Danjovic/JoyKid/sources/PIC/JoyKidProtocol/Test/pic16f688.h

/*
 * This declarations of the PIC16F688 MCU.
 *
 * This file is part of the GNU PIC library for SDCC, originally
 * created by Molnar Karoly <molnarkaroly@users.sf.net> 2012.
 *
 * This file is generated automatically by the cinc2h.pl, 2012-11-01 17:30:08 UTC.
 *
 * SDCC is licensed under the GNU Public license (GPL) v2. Note that
 * this license covers the code to the compiler and other executables,
 * but explicitly does not cover any code or objects generated by sdcc.
 *
 * For pic device libraries and header files which are derived from
 * Microchip header (.inc) and linker script (.lkr) files Microchip
 * requires that "The header files should state that they are only to be
 * used with authentic Microchip devices" which makes them incompatible
 * with the GPL. Pic device libraries and header files are located at
 * non-free/lib and non-free/include directories respectively.
 * Sdcc should be run with the --use-non-free command line option in
 * order to include non-free header files and libraries.
 *
 * See http://sdcc.sourceforge.net/ for the latest information on sdcc.
 */

#ifndef __PIC16F688_H__
#define __PIC16F688_H__

//==============================================================================
//
//	Register Addresses
//
//==============================================================================

#ifndef NO_ADDR_DEFINES

#define INDF_ADDR               0x0000
#define TMR0_ADDR               0x0001
#define PCL_ADDR                0x0002
#define STATUS_ADDR             0x0003
#define FSR_ADDR                0x0004
#define PORTA_ADDR              0x0005
#define PORTC_ADDR              0x0007
#define PCLATH_ADDR             0x000A
#define INTCON_ADDR             0x000B
#define PIR1_ADDR               0x000C
#define TMR1_ADDR               0x000E
#define TMR1L_ADDR              0x000E
#define TMR1H_ADDR              0x000F
#define T1CON_ADDR              0x0010
#define BAUDCTL_ADDR            0x0011
#define SPBRGH_ADDR             0x0012
#define SPBRG_ADDR              0x0013
#define RCREG_ADDR              0x0014
#define TXREG_ADDR              0x0015
#define TXSTA_ADDR              0x0016
#define RCSTA_ADDR              0x0017
#define WDTCON_ADDR             0x0018
#define CMCON0_ADDR             0x0019
#define CMCON1_ADDR             0x001A
#define ADRESH_ADDR             0x001E
#define ADCON0_ADDR             0x001F
#define OPTION_REG_ADDR         0x0081
#define TRISA_ADDR              0x0085
#define TRISC_ADDR              0x0087
#define PIE1_ADDR               0x008C
#define PCON_ADDR               0x008E
#define OSCCON_ADDR             0x008F
#define OSCTUNE_ADDR            0x0090
#define ANSEL_ADDR              0x0091
#define WPU_ADDR                0x0095
#define WPUA_ADDR               0x0095
#define IOC_ADDR                0x0096
#define IOCA_ADDR               0x0096
#define EEDATH_ADDR             0x0097
#define EEADRH_ADDR             0x0098
#define VRCON_ADDR              0x0099
#define EEDAT_ADDR              0x009A
#define EEDATA_ADDR             0x009A
#define EEADR_ADDR              0x009B
#define EECON1_ADDR             0x009C
#define EECON2_ADDR             0x009D
#define ADRESL_ADDR             0x009E
#define ADCON1_ADDR             0x009F

#endif // #ifndef NO_ADDR_DEFINES

//==============================================================================
//
//	Register Definitions
//
//==============================================================================

extern __at(0x0000) __sfr INDF;
extern __at(0x0001) __sfr TMR0;
extern __at(0x0002) __sfr PCL;

//==============================================================================
//        STATUS Bits

extern __at(0x0003) __sfr STATUS;

typedef union
  {
  struct
    {
    unsigned C                  : 1;
    unsigned DC                 : 1;
    unsigned Z                  : 1;
    unsigned NOT_PD             : 1;
    unsigned NOT_TO             : 1;
    unsigned RP0                : 1;
    unsigned RP1                : 1;
    unsigned IRP                : 1;
    };

  struct
    {
    unsigned                    : 5;
    unsigned RP                 : 2;
    unsigned                    : 1;
    };
  } __STATUSbits_t;

extern __at(0x0003) volatile __STATUSbits_t STATUSbits;

#define _C                      0x01
#define _DC                     0x02
#define _Z                      0x04
#define _NOT_PD                 0x08
#define _NOT_TO                 0x10
#define _RP0                    0x20
#define _RP1                    0x40
#define _IRP                    0x80

//==============================================================================

extern __at(0x0004) __sfr FSR;

//==============================================================================
//        PORTA Bits

extern __at(0x0005) __sfr PORTA;

typedef union
  {
  struct
    {
    unsigned RA0                : 1;
    unsigned RA1                : 1;
    unsigned RA2                : 1;
    unsigned RA3                : 1;
    unsigned RA4                : 1;
    unsigned RA5                : 1;
    unsigned                    : 1;
    unsigned                    : 1;
    };

  struct
    {
    unsigned RA                 : 6;
    unsigned                    : 2;
    };
  } __PORTAbits_t;

extern __at(0x0005) volatile __PORTAbits_t PORTAbits;

#define _RA0                    0x01
#define _RA1                    0x02
#define _RA2                    0x04
#define _RA3                    0x08
#define _RA4                    0x10
#define _RA5                    0x20

//==============================================================================


//==============================================================================
//        PORTC Bits

extern __at(0x0007) __sfr PORTC;

typedef union
  {
  struct
    {
    unsigned RC0                : 1;
    unsigned RC1                : 1;
    unsigned RC2                : 1;
    unsigned RC3                : 1;
    unsigned RC4                : 1;
    unsigned RC5                : 1;
    unsigned                    : 1;
    unsigned                    : 1;
    };

  struct
    {
    unsigned RC                 : 6;
    unsigned                    : 2;
    };
  } __PORTCbits_t;

extern __at(0x0007) volatile __PORTCbits_t PORTCbits;

#define _RC0                    0x01
#define _RC1                    0x02
#define _RC2                    0x04
#define _RC3                    0x08
#define _RC4                    0x10
#define _RC5                    0x20

//==============================================================================

extern __at(0x000A) __sfr PCLATH;

//==============================================================================
//        INTCON Bits

extern __at(0x000B) __sfr INTCON;

typedef union
  {
  struct
    {
    unsigned RAIF               : 1;
    unsigned INTF               : 1;
    unsigned T0IF               : 1;
    unsigned RAIE               : 1;
    unsigned INTE               : 1;
    unsigned T0IE               : 1;
    unsigned PEIE               : 1;
    unsigned GIE                : 1;
    };

  struct
    {
    unsigned                    : 1;
    unsigned                    : 1;
    unsigned TMR0IF             : 1;
    unsigned                    : 1;
    unsigned                    : 1;
    unsigned TMR0IE             : 1;
    unsigned                    : 1;
    unsigned                    : 1;
    };
  } __INTCONbits_t;

extern __at(0x000B) volatile __INTCONbits_t INTCONbits;

#define _RAIF                   0x01
#define _INTF                   0x02
#define _T0IF                   0x04
#define _TMR0IF                 0x04
#define _RAIE                   0x08
#define _INTE                   0x10
#define _T0IE                   0x20
#define _TMR0IE                 0x20
#define _PEIE                   0x40
#define _GIE                    0x80

//==============================================================================


//==============================================================================
//        PIR1 Bits

extern __at(0x000C) __sfr PIR1;

typedef union
  {
  struct
    {
    unsigned TMR1IF             : 1;
    unsigned TXIF               : 1;
    unsigned OSFIF              : 1;
    unsigned C1IF               : 1;
    unsigned C2IF               : 1;
    unsigned RCIF               : 1;
    unsigned ADIF               : 1;
    unsigned EEIF               : 1;
    };

  struct
    {
    unsigned T1IF               : 1;
    unsigned                    : 1;
    unsigned                    : 1;
    unsigned                    : 1;
    unsigned                    : 1;
    unsigned                    : 1;
    unsigned                    : 1;
    unsigned                    : 1;
    };
  } __PIR1bits_t;

extern __at(0x000C) volatile __PIR1bits_t PIR1bits;

#define _TMR1IF                 0x01
#define _T1IF                   0x01
#define _TXIF                   0x02
#define _OSFIF                  0x04
#define _C1IF                   0x08
#define _C2IF                   0x10
#define _RCIF                   0x20
#define _ADIF                   0x40
#define _EEIF                   0x80

//==============================================================================

extern __at(0x000E) __sfr TMR1;
extern __at(0x000E) __sfr TMR1L;
extern __at(0x000F) __sfr TMR1H;

//==============================================================================
//        T1CON Bits

extern __at(0x0010) __sfr T1CON;

typedef union
  {
  struct
    {
    unsigned TMR1ON             : 1;
    unsigned TMR1CS             : 1;
    unsigned NOT_T1SYNC         : 1;
    unsigned T1OSCEN            : 1;
    unsigned T1CKPS0            : 1;
    unsigned T1CKPS1            : 1;
    unsigned TMR1GE             : 1;
    unsigned T1GINV             : 1;
    };

  struct
    {
    unsigned                    : 4;
    unsigned T1CKPS             : 2;
    unsigned                    : 2;
    };
  } __T1CONbits_t;

extern __at(0x0010) volatile __T1CONbits_t T1CONbits;

#define _TMR1ON                 0x01
#define _TMR1CS                 0x02
#define _NOT_T1SYNC             0x04
#define _T1OSCEN                0x08
#define _T1CKPS0                0x10
#define _T1CKPS1                0x20
#define _TMR1GE                 0x40
#define _T1GINV                 0x80

//==============================================================================


//==============================================================================
//        BAUDCTL Bits

extern __at(0x0011) __sfr BAUDCTL;

#define BAUDCON BAUDCTL

typedef struct
  {
  unsigned ABDEN                : 1;
  unsigned WUE                  : 1;
  unsigned                      : 1;
  unsigned BRG16                : 1;
  unsigned SCKP                 : 1;
  unsigned                      : 1;
  unsigned RCIDL                : 1;
  unsigned ABDOVF               : 1;
  } __BAUDCTLbits_t;

extern __at(0x0011) volatile __BAUDCTLbits_t BAUDCTLbits;

#define BAUDCONbits BAUDCTLbits

#define _ABDEN                  0x01
#define _WUE                    0x02
#define _BRG16                  0x08
#define _SCKP                   0x10
#define _RCIDL                  0x40
#define _ABDOVF                 0x80

//==============================================================================

extern __at(0x0012) __sfr SPBRGH;
extern __at(0x0013) __sfr SPBRG;
extern __at(0x0014) __sfr RCREG;
extern __at(0x0015) __sfr TXREG;

//==============================================================================
//        TXSTA Bits

extern __at(0x0016) __sfr TXSTA;

typedef struct
  {
  unsigned TX9D                 : 1;
  unsigned TRMT                 : 1;
  unsigned BRGH                 : 1;
  unsigned SENDB                : 1;
  unsigned SYNC                 : 1;
  unsigned TXEN                 : 1;
  unsigned TX9                  : 1;
  unsigned CSRC                 : 1;
  } __TXSTAbits_t;

extern __at(0x0016) volatile __TXSTAbits_t TXSTAbits;

#define _TX9D                   0x01
#define _TRMT                   0x02
#define _BRGH                   0x04
#define _SENDB                  0x08
#define _SYNC                   0x10
#define _TXEN                   0x20
#define _TX9                    0x40
#define _CSRC                   0x80

//==============================================================================


//==============================================================================
//        RCSTA Bits

extern __at(0x0017) __sfr RCSTA;

typedef struct
  {
  unsigned RX9D                 : 1;
  unsigned OERR                 : 1;
  unsigned FERR                 : 1;
  unsigned ADDEN                : 1;
  unsigned CREN                 : 1;
  unsigned SREN                 : 1;
  unsigned RX9                  : 1;
  unsigned SPEN                 : 1;
  } __RCSTAbits_t;

extern __at(0x0017) volatile __RCSTAbits_t RCSTAbits;

#define _RX9D                   0x01
#define _OERR                   0x02
#define _FERR                   0x04
#define _ADDEN                  0x08
#define _CREN                   0x10
#define _SREN                   0x20
#define _RX9                    0x40
#define _SPEN                   0x80

//==============================================================================


//==============================================================================
//        WDTCON Bits

extern __at(0x0018) __sfr WDTCON;

typedef union
  {
  struct
    {
    unsigned SWDTEN             : 1;
    unsigned WDTPS0             : 1;
    unsigned WDTPS1             : 1;
    unsigned WDTPS2             : 1;
    unsigned WDTPS3             : 1;
    unsigned                    : 1;
    unsigned                    : 1;
    unsigned                    : 1;
    };

  struct
    {
    unsigned                    : 1;
    unsigned WDTPS              : 4;
    unsigned                    : 3;
    };
  } __WDTCONbits_t;

extern __at(0x0018) volatile __WDTCONbits_t WDTCONbits;

#define _SWDTEN                 0x01
#define _WDTPS0                 0x02
#define _WDTPS1                 0x04
#define _WDTPS2                 0x08
#define _WDTPS3                 0x10

//==============================================================================


//==============================================================================
//        CMCON0 Bits

extern __at(0x0019) __sfr CMCON0;

typedef union
  {
  struct
    {
    unsigned CM0                : 1;
    unsigned CM1                : 1;
    unsigned CM2                : 1;
    unsigned CIS                : 1;
    unsigned C1INV              : 1;
    unsigned C2INV              : 1;
    unsigned C1OUT              : 1;
    unsigned C2OUT              : 1;
    };

  struct
    {
    unsigned CM                 : 3;
    unsigned                    : 5;
    };
  } __CMCON0bits_t;

extern __at(0x0019) volatile __CMCON0bits_t CMCON0bits;

#define _CM0                    0x01
#define _CM1                    0x02
#define _CM2                    0x04
#define _CIS                    0x08
#define _C1INV                  0x10
#define _C2INV                  0x20
#define _C1OUT                  0x40
#define _C2OUT                  0x80

//==============================================================================


//==============================================================================
//        CMCON1 Bits

extern __at(0x001A) __sfr CMCON1;

typedef struct
  {
  unsigned C2SYNC               : 1;
  unsigned T1GSS                : 1;
  unsigned                      : 1;
  unsigned                      : 1;
  unsigned                      : 1;
  unsigned                      : 1;
  unsigned                      : 1;
  unsigned                      : 1;
  } __CMCON1bits_t;

extern __at(0x001A) volatile __CMCON1bits_t CMCON1bits;

#define _C2SYNC                 0x01
#define _T1GSS                  0x02

//==============================================================================

extern __at(0x001E) __sfr ADRESH;

//==============================================================================
//        ADCON0 Bits

extern __at(0x001F) __sfr ADCON0;

typedef union
  {
  struct
    {
    unsigned ADON               : 1;
    unsigned GO_NOT_DONE        : 1;
    unsigned CHS0               : 1;
    unsigned CHS1               : 1;
    unsigned CHS2               : 1;
    unsigned                    : 1;
    unsigned VCFG               : 1;
    unsigned ADFM               : 1;
    };

  struct
    {
    unsigned                    : 1;
    unsigned GO                 : 1;
    unsigned                    : 1;
    unsigned                    : 1;
    unsigned                    : 1;
    unsigned                    : 1;
    unsigned                    : 1;
    unsigned                    : 1;
    };

  struct
    {
    unsigned                    : 1;
    unsigned NOT_DONE           : 1;
    unsigned                    : 1;
    unsigned                    : 1;
    unsigned                    : 1;
    unsigned                    : 1;
    unsigned                    : 1;
    unsigned                    : 1;
    };

  struct
    {
    unsigned                    : 1;
    unsigned GO_DONE            : 1;
    unsigned                    : 1;
    unsigned                    : 1;
    unsigned                    : 1;
    unsigned                    : 1;
    unsigned                    : 1;
    unsigned                    : 1;
    };

  struct
    {
    unsigned                    : 2;
    unsigned CHS                : 3;
    unsigned                    : 3;
    };
  } __ADCON0bits_t;

extern __at(0x001F) volatile __ADCON0bits_t ADCON0bits;

#define _ADON                   0x01
#define _GO_NOT_DONE            0x02
#define _GO                     0x02
#define _NOT_DONE               0x02
#define _GO_DONE                0x02
#define _CHS0                   0x04
#define _CHS1                   0x08
#define _CHS2                   0x10
#define _VCFG                   0x40
#define _ADFM                   0x80

//==============================================================================


//==============================================================================
//        OPTION_REG Bits

extern __at(0x0081) __sfr OPTION_REG;

typedef union
  {
  struct
    {
    unsigned PS0                : 1;
    unsigned PS1                : 1;
    unsigned PS2                : 1;
    unsigned PSA                : 1;
    unsigned T0SE               : 1;
    unsigned T0CS               : 1;
    unsigned INTEDG             : 1;
    unsigned NOT_RAPU           : 1;
    };

  struct
    {
    unsigned PS                 : 3;
    unsigned                    : 5;
    };
  } __OPTION_REGbits_t;

extern __at(0x0081) volatile __OPTION_REGbits_t OPTION_REGbits;

#define _PS0                    0x01
#define _PS1                    0x02
#define _PS2                    0x04
#define _PSA                    0x08
#define _T0SE                   0x10
#define _T0CS                   0x20
#define _INTEDG                 0x40
#define _NOT_RAPU               0x80

//==============================================================================


//==============================================================================
//        TRISA Bits

extern __at(0x0085) __sfr TRISA;

typedef union
  {
  struct
    {
    unsigned TRISA0             : 1;
    unsigned TRISA1             : 1;
    unsigned TRISA2             : 1;
    unsigned TRISA3             : 1;
    unsigned TRISA4             : 1;
    unsigned TRISA5             : 1;
    unsigned                    : 1;
    unsigned                    : 1;
    };

  struct
    {
    unsigned TRISA              : 6;
    unsigned                    : 2;
    };
  } __TRISAbits_t;

extern __at(0x0085) volatile __TRISAbits_t TRISAbits;

#define _TRISA0                 0x01
#define _TRISA1                 0x02
#define _TRISA2                 0x04
#define _TRISA3                 0x08
#define _TRISA4                 0x10
#define _TRISA5                 0x20

//==============================================================================


//==============================================================================
//        TRISC Bits

extern __at(0x0087) __sfr TRISC;

typedef union
  {
  struct
    {
    unsigned TRISC0             : 1;
    unsigned TRISC1             : 1;
    unsigned TRISC2             : 1;
    unsigned TRISC3             : 1;
    unsigned TRISC4             : 1;
    unsigned TRISC5             : 1;
    unsigned                    : 1;
    unsigned                    : 1;
    };

  struct
    {
    unsigned TRISC              : 6;
    unsigned                    : 2;
    };
  } __TRISCbits_t;

extern __at(0x0087) volatile __TRISCbits_t TRISCbits;

#define _TRISC0                 0x01
#define _TRISC1                 0x02
#define _TRISC2                 0x04
#define _TRISC3                 0x08
#define _TRISC4                 0x10
#define _TRISC5                 0x20

//==============================================================================


//==============================================================================
//        PIE1 Bits

extern __at(0x008C) __sfr PIE1;

typedef union
  {
  struct
    {
    unsigned TMR1IE             : 1;
    unsigned TXIE               : 1;
    unsigned OSFIE              : 1;
    unsigned C1IE               : 1;
    unsigned C2IE               : 1;
    unsigned RCIE               : 1;
    unsigned ADIE               : 1;
    unsigned EEIE               : 1;
    };

  struct
    {
    unsigned T1IE               : 1;
    unsigned                    : 1;
    unsigned                    : 1;
    unsigned                    : 1;
    unsigned                    : 1;
    unsigned                    : 1;
    unsigned                    : 1;
    unsigned                    : 1;
    };
  } __PIE1bits_t;

extern __at(0x008C) volatile __PIE1bits_t PIE1bits;

#define _TMR1IE                 0x01
#define _T1IE                   0x01
#define _TXIE                   0x02
#define _OSFIE                  0x04
#define _C1IE                   0x08
#define _C2IE                   0x10
#define _RCIE                   0x20
#define _ADIE                   0x40
#define _EEIE                   0x80

//==============================================================================


//==============================================================================
//        PCON Bits

extern __at(0x008E) __sfr PCON;

typedef union
  {
  struct
    {
    unsigned NOT_BOR            : 1;
    unsigned NOT_POR            : 1;
    unsigned                    : 1;
    unsigned                    : 1;
    unsigned SBODEN             : 1;
    unsigned ULPWUE             : 1;
    unsigned                    : 1;
    unsigned                    : 1;
    };

  struct
    {
    unsigned NOT_BOD            : 1;
    unsigned                    : 1;
    unsigned                    : 1;
    unsigned                    : 1;
    unsigned                    : 1;
    unsigned                    : 1;
    unsigned                    : 1;
    unsigned                    : 1;
    };
  } __PCONbits_t;

extern __at(0x008E) volatile __PCONbits_t PCONbits;

#define _NOT_BOR                0x01
#define _NOT_BOD                0x01
#define _NOT_POR                0x02
#define _SBODEN                 0x10
#define _ULPWUE                 0x20

//==============================================================================


//==============================================================================
//        OSCCON Bits

extern __at(0x008F) __sfr OSCCON;

typedef union
  {
  struct
    {
    unsigned SCS                : 1;
    unsigned LTS                : 1;
    unsigned HTS                : 1;
    unsigned OSTS               : 1;
    unsigned IRCF0              : 1;
    unsigned IRCF1              : 1;
    unsigned IRCF2              : 1;
    unsigned                    : 1;
    };

  struct
    {
    unsigned                    : 4;
    unsigned IRCF               : 3;
    unsigned                    : 1;
    };
  } __OSCCONbits_t;

extern __at(0x008F) volatile __OSCCONbits_t OSCCONbits;

#define _SCS                    0x01
#define _LTS                    0x02
#define _HTS                    0x04
#define _OSTS                   0x08
#define _IRCF0                  0x10
#define _IRCF1                  0x20
#define _IRCF2                  0x40

//==============================================================================


//==============================================================================
//        OSCTUNE Bits

extern __at(0x0090) __sfr OSCTUNE;

typedef union
  {
  struct
    {
    unsigned TUN0               : 1;
    unsigned TUN1               : 1;
    unsigned TUN2               : 1;
    unsigned TUN3               : 1;
    unsigned TUN4               : 1;
    unsigned                    : 1;
    unsigned                    : 1;
    unsigned                    : 1;
    };

  struct
    {
    unsigned TUN                : 5;
    unsigned                    : 3;
    };
  } __OSCTUNEbits_t;

extern __at(0x0090) volatile __OSCTUNEbits_t OSCTUNEbits;

#define _TUN0                   0x01
#define _TUN1                   0x02
#define _TUN2                   0x04
#define _TUN3                   0x08
#define _TUN4                   0x10

//==============================================================================


//==============================================================================
//        ANSEL Bits

extern __at(0x0091) __sfr ANSEL;

typedef struct
  {
  unsigned ANS0                 : 1;
  unsigned ANS1                 : 1;
  unsigned ANS2                 : 1;
  unsigned ANS3                 : 1;
  unsigned ANS4                 : 1;
  unsigned ANS5                 : 1;
  unsigned ANS6                 : 1;
  unsigned ANS7                 : 1;
  } __ANSELbits_t;

extern __at(0x0091) volatile __ANSELbits_t ANSELbits;

#define _ANS0                   0x01
#define _ANS1                   0x02
#define _ANS2                   0x04
#define _ANS3                   0x08
#define _ANS4                   0x10
#define _ANS5                   0x20
#define _ANS6                   0x40
#define _ANS7                   0x80

//==============================================================================


//==============================================================================
//        WPU Bits

extern __at(0x0095) __sfr WPU;

typedef union
  {
  struct
    {
    unsigned WPUA0              : 1;
    unsigned WPUA1              : 1;
    unsigned WPUA2              : 1;
    unsigned                    : 1;
    unsigned WPUA4              : 1;
    unsigned WPUA5              : 1;
    unsigned                    : 1;
    unsigned                    : 1;
    };

  struct
    {
    unsigned WPU0               : 1;
    unsigned WPU1               : 1;
    unsigned WPU2               : 1;
    unsigned                    : 1;
    unsigned WPU4               : 1;
    unsigned WPU5               : 1;
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
    unsigned IOC3               : 1;
    unsigned IOC4               : 1;
    unsigned IOC5               : 1;
    unsigned                    : 1;
    unsigned                    : 1;
    };

  struct
    {
    unsigned IOCA               : 6;
    unsigned                    : 2;
    };

  struct
    {
    unsigned IOC                : 6;
    unsigned                    : 2;
    };
  } __IOCAbits_t;

extern __at(0x0096) volatile __IOCAbits_t IOCAbits;

#define _IOCA_IOCA0             0x01
#define _IOCA_IOC0              0x01
#define _IOCA_IOCA1             0x02
#define _IOCA_IOC1              0x02
#define _IOCA_IOCA2             0x04
#define _IOCA_IOC2              0x04
#define _IOCA_IOCA3             0x08
#define _IOCA_IOC3              0x08
#define _IOCA_IOCA4             0x10
#define _IOCA_IOC4              0x10
#define _IOCA_IOCA5             0x20
#define _IOCA_IOC5              0x20

//==============================================================================

extern __at(0x0097) __sfr EEDATH;
extern __at(0x0098) __sfr EEADRH;

//==============================================================================
//        VRCON Bits

extern __at(0x0099) __sfr VRCON;

typedef union
  {
  struct
    {
    unsigned VR0                : 1;
    unsigned VR1                : 1;
    unsigned VR2                : 1;
    unsigned VR3                : 1;
    unsigned                    : 1;
    unsigned VRR                : 1;
    unsigned                    : 1;
    unsigned VREN               : 1;
    };

  struct
    {
    unsigned VR                 : 4;
    unsigned                    : 4;
    };
  } __VRCONbits_t;

extern __at(0x0099) volatile __VRCONbits_t VRCONbits;

#define _VR0                    0x01
#define _VR1                    0x02
#define _VR2                    0x04
#define _VR3                    0x08
#define _VRR                    0x20
#define _VREN                   0x80

//==============================================================================

extern __at(0x009A) __sfr EEDAT;
extern __at(0x009A) __sfr EEDATA;
extern __at(0x009B) __sfr EEADR;

//==============================================================================
//        EECON1 Bits

extern __at(0x009C) __sfr EECON1;

typedef struct
  {
  unsigned RD                   : 1;
  unsigned WR                   : 1;
  unsigned WREN                 : 1;
  unsigned WRERR                : 1;
  unsigned                      : 1;
  unsigned                      : 1;
  unsigned                      : 1;
  unsigned EEPGD                : 1;
  } __EECON1bits_t;

extern __at(0x009C) volatile __EECON1bits_t EECON1bits;

#define _RD                     0x01
#define _WR                     0x02
#define _WREN                   0x04
#define _WRERR                  0x08
#define _EEPGD                  0x80

//==============================================================================

extern __at(0x009D) __sfr EECON2;
extern __at(0x009E) __sfr ADRESL;

//==============================================================================
//        ADCON1 Bits

extern __at(0x009F) __sfr ADCON1;

typedef union
  {
  struct
    {
    unsigned                    : 1;
    unsigned                    : 1;
    unsigned                    : 1;
    unsigned                    : 1;
    unsigned ADCS0              : 1;
    unsigned ADCS1              : 1;
    unsigned ADCS2              : 1;
    unsigned                    : 1;
    };

  struct
    {
    unsigned                    : 4;
    unsigned ADCS               : 3;
    unsigned                    : 1;
    };
  } __ADCON1bits_t;

extern __at(0x009F) volatile __ADCON1bits_t ADCON1bits;

#define _ADCS0                  0x10
#define _ADCS1                  0x20
#define _ADCS2                  0x40

//==============================================================================


//==============================================================================
//
//        Configuration Bits
//
//==============================================================================

#define _CONFIG                 0x2007

//----------------------------- CONFIG Options -------------------------------

#define _FOSC_LP                0x3FF8  // LP oscillator: Low-power crystal on RA4/OSC2/CLKOUT and RA5/OSC1/CLKIN.
#define _LP_OSC                 0x3FF8  // LP oscillator: Low-power crystal on RA4/OSC2/CLKOUT and RA5/OSC1/CLKIN.
#define _FOSC_XT                0x3FF9  // XT oscillator: Crystal/resonator on RA4/OSC2/CLKOUT and RA5/OSC1/CLKINT.
#define _XT_OSC                 0x3FF9  // XT oscillator: Crystal/resonator on RA4/OSC2/CLKOUT and RA5/OSC1/CLKINT.
#define _FOSC_HS                0x3FFA  // HS oscillator: High-speed crystal/resonator on RA4/OSC2/CLKOUT and RA5/OSC1/CLKIN.
#define _HS_OSC                 0x3FFA  // HS oscillator: High-speed crystal/resonator on RA4/OSC2/CLKOUT and RA5/OSC1/CLKIN.
#define _FOSC_EC                0x3FFB  // EC: I/O function on RA4/OSC2/CLKOUT pin, CLKIN on RA5/OSC1/CLKIN.
#define _EC_OSC                 0x3FFB  // EC: I/O function on RA4/OSC2/CLKOUT pin, CLKIN on RA5/OSC1/CLKIN.
#define _FOSC_INTOSCIO          0x3FFC  // INTOSCIO oscillator: I/O function on RA4/OSC2/CLKOUT pin, I/O function on RA5/OSC1/CLKIN.
#define _INTOSCIO               0x3FFC  // INTOSCIO oscillator: I/O function on RA4/OSC2/CLKOUT pin, I/O function on RA5/OSC1/CLKIN.
#define _INTRC_OSC_NOCLKOUT     0x3FFC  // INTOSCIO oscillator: I/O function on RA4/OSC2/CLKOUT pin, I/O function on RA5/OSC1/CLKIN.
#define _FOSC_INTOSCCLK         0x3FFD  // INTOSC oscillator: CLKOUT function on RA4/OSC2/CLKOUT pin, I/O function on RA5/OSC1/CLKIN.
#define _INTOSC                 0x3FFD  // INTOSC oscillator: CLKOUT function on RA4/OSC2/CLKOUT pin, I/O function on RA5/OSC1/CLKIN.
#define _INTRC_OSC_CLKOUT       0x3FFD  // INTOSC oscillator: CLKOUT function on RA4/OSC2/CLKOUT pin, I/O function on RA5/OSC1/CLKIN.
#define _FOSC_EXTRCIO           0x3FFE  // EXTRCIO oscillator: External RC on RA5/OSC1/CLKIN, I/O function on RA4/OSC2/CLKOUT pin.
#define _EXTRCIO                0x3FFE  // EXTRCIO oscillator: External RC on RA5/OSC1/CLKIN, I/O function on RA4/OSC2/CLKOUT pin.
#define _EXTRC_OSC_NOCLKOUT     0x3FFE  // EXTRCIO oscillator: External RC on RA5/OSC1/CLKIN, I/O function on RA4/OSC2/CLKOUT pin.
#define _FOSC_EXTRCCLK          0x3FFF  // EXTRC oscillator: External RC on RA5/OSC1/CLKIN, CLKOUT function on RA4/OSC2/CLKOUT pin.
#define _EXTRC                  0x3FFF  // EXTRC oscillator: External RC on RA5/OSC1/CLKIN, CLKOUT function on RA4/OSC2/CLKOUT pin.
#define _EXTRC_OSC_CLKOUT       0x3FFF  // EXTRC oscillator: External RC on RA5/OSC1/CLKIN, CLKOUT function on RA4/OSC2/CLKOUT pin.
#define _WDTE_OFF               0x3FF7  // WDT disabled.
#define _WDT_OFF                0x3FF7  // WDT disabled.
#define _WDTE_ON                0x3FFF  // WDT enabled.
#define _WDT_ON                 0x3FFF  // WDT enabled.
#define _PWRTE_ON               0x3FEF  // PWRT enabled.
#define _PWRTE_OFF              0x3FFF  // PWRT disabled.
#define _MCLRE_OFF              0x3FDF  // MCLR pin function is digital input, MCLR internally tied to VDD.
#define _MCLRE_ON               0x3FFF  // MCLR pin function is MCLR.
#define _CP_ON                  0x3FBF  // Program memory code protection is enabled.
#define _CP_OFF                 0x3FFF  // Program memory code protection is disabled.
#define _CPD_ON                 0x3F7F  // Data memory code protection is enabled.
#define _CPD_OFF                0x3FFF  // Data memory code protection is disabled.
#define _BOREN_OFF              0x3CFF  // BOR disabled.
#define _BOD_OFF                0x3CFF  // BOR disabled.
#define _BOR_OFF                0x3CFF  // BOR disabled.
#define _BOREN_SBODEN           0x3DFF  // BOR controlled by SBOREN bit of the PCON register.
#define _BOD_SBODEN             0x3DFF  // BOR controlled by SBOREN bit of the PCON register.
#define _BOR_SBODEN             0x3DFF  // BOR controlled by SBOREN bit of the PCON register.
#define _BOREN_NSLEEP           0x3EFF  // BOR enabled during operation and disabled in Sleep.
#define _BOD_NSLEEP             0x3EFF  // BOR enabled during operation and disabled in Sleep.
#define _BOR_NSLEEP             0x3EFF  // BOR enabled during operation and disabled in Sleep.
#define _BOREN_ON               0x3FFF  // BOR enabled.
#define _BOD_ON                 0x3FFF  // BOR enabled.
#define _BOR_ON                 0x3FFF  // BOR enabled.
#define _IESO_OFF               0x3BFF  // Internal External Switchover mode is disabled.
#define _IESO_ON                0x3FFF  // Internal External Switchover mode is enabled.
#define _FCMEN_OFF              0x37FF  // Fail-Safe Clock Monitor is disabled.
#define _FCMEN_ON               0x3FFF  // Fail-Safe Clock Monitor is enabled.

//==============================================================================

#define _DEVID1                 0x2006

#define _IDLOC0                 0x2000
#define _IDLOC1                 0x2001
#define _IDLOC2                 0x2002
#define _IDLOC3                 0x2003

//==============================================================================

#ifndef NO_BIT_DEFINES

#define ADON                    ADCON0bits.ADON                 // bit 0
#define GO_NOT_DONE             ADCON0bits.GO_NOT_DONE          // bit 1, shadows bit in ADCON0bits
#define GO                      ADCON0bits.GO                   // bit 1, shadows bit in ADCON0bits
#define NOT_DONE                ADCON0bits.NOT_DONE             // bit 1, shadows bit in ADCON0bits
#define GO_DONE                 ADCON0bits.GO_DONE              // bit 1, shadows bit in ADCON0bits
#define CHS0                    ADCON0bits.CHS0                 // bit 2
#define CHS1                    ADCON0bits.CHS1                 // bit 3
#define CHS2                    ADCON0bits.CHS2                 // bit 4
#define VCFG                    ADCON0bits.VCFG                 // bit 6
#define ADFM                    ADCON0bits.ADFM                 // bit 7

#define ADCS0                   ADCON1bits.ADCS0                // bit 4
#define ADCS1                   ADCON1bits.ADCS1                // bit 5
#define ADCS2                   ADCON1bits.ADCS2                // bit 6

#define ANS0                    ANSELbits.ANS0                  // bit 0
#define ANS1                    ANSELbits.ANS1                  // bit 1
#define ANS2                    ANSELbits.ANS2                  // bit 2
#define ANS3                    ANSELbits.ANS3                  // bit 3
#define ANS4                    ANSELbits.ANS4                  // bit 4
#define ANS5                    ANSELbits.ANS5                  // bit 5
#define ANS6                    ANSELbits.ANS6                  // bit 6
#define ANS7                    ANSELbits.ANS7                  // bit 7

#define ABDEN                   BAUDCTLbits.ABDEN               // bit 0
#define WUE                     BAUDCTLbits.WUE                 // bit 1
#define BRG16                   BAUDCTLbits.BRG16               // bit 3
#define SCKP                    BAUDCTLbits.SCKP                // bit 4
#define RCIDL                   BAUDCTLbits.RCIDL               // bit 6
#define ABDOVF                  BAUDCTLbits.ABDOVF              // bit 7

#define CM0                     CMCON0bits.CM0                  // bit 0
#define CM1                     CMCON0bits.CM1                  // bit 1
#define CM2                     CMCON0bits.CM2                  // bit 2
#define CIS                     CMCON0bits.CIS                  // bit 3
#define C1INV                   CMCON0bits.C1INV                // bit 4
#define C2INV                   CMCON0bits.C2INV                // bit 5
#define C1OUT                   CMCON0bits.C1OUT                // bit 6
#define C2OUT                   CMCON0bits.C2OUT                // bit 7

#define C2SYNC                  CMCON1bits.C2SYNC               // bit 0
#define T1GSS                   CMCON1bits.T1GSS                // bit 1

#define RD                      EECON1bits.RD                   // bit 0
#define WR                      EECON1bits.WR                   // bit 1
#define WREN                    EECON1bits.WREN                 // bit 2
#define WRERR                   EECON1bits.WRERR                // bit 3
#define EEPGD                   EECON1bits.EEPGD                // bit 7

#define RAIF                    INTCONbits.RAIF                 // bit 0
#define INTF                    INTCONbits.INTF                 // bit 1
#define T0IF                    INTCONbits.T0IF                 // bit 2, shadows bit in INTCONbits
#define TMR0IF                  INTCONbits.TMR0IF               // bit 2, shadows bit in INTCONbits
#define RAIE                    INTCONbits.RAIE                 // bit 3
#define INTE                    INTCONbits.INTE                 // bit 4
#define T0IE                    INTCONbits.T0IE                 // bit 5, shadows bit in INTCONbits
#define TMR0IE                  INTCONbits.TMR0IE               // bit 5, shadows bit in INTCONbits
#define PEIE                    INTCONbits.PEIE                 // bit 6
#define GIE                     INTCONbits.GIE                  // bit 7

#define IOCA0                   IOCbits.IOCA0                   // bit 0, shadows bit in IOCbits
#define IOC0                    IOCbits.IOC0                    // bit 0, shadows bit in IOCbits
#define IOCA1                   IOCbits.IOCA1                   // bit 1, shadows bit in IOCbits
#define IOC1                    IOCbits.IOC1                    // bit 1, shadows bit in IOCbits
#define IOCA2                   IOCbits.IOCA2                   // bit 2, shadows bit in IOCbits
#define IOC2                    IOCbits.IOC2                    // bit 2, shadows bit in IOCbits
#define IOCA3                   IOCbits.IOCA3                   // bit 3, shadows bit in IOCbits
#define IOC3                    IOCbits.IOC3                    // bit 3, shadows bit in IOCbits
#define IOCA4                   IOCbits.IOCA4                   // bit 4, shadows bit in IOCbits
#define IOC4                    IOCbits.IOC4                    // bit 4, shadows bit in IOCbits
#define IOCA5                   IOCbits.IOCA5                   // bit 5, shadows bit in IOCbits
#define IOC5                    IOCbits.IOC5                    // bit 5, shadows bit in IOCbits

#define PS0                     OPTION_REGbits.PS0              // bit 0
#define PS1                     OPTION_REGbits.PS1              // bit 1
#define PS2                     OPTION_REGbits.PS2              // bit 2
#define PSA                     OPTION_REGbits.PSA              // bit 3
#define T0SE                    OPTION_REGbits.T0SE             // bit 4
#define T0CS                    OPTION_REGbits.T0CS             // bit 5
#define INTEDG                  OPTION_REGbits.INTEDG           // bit 6
#define NOT_RAPU                OPTION_REGbits.NOT_RAPU         // bit 7

#define SCS                     OSCCONbits.SCS                  // bit 0
#define LTS                     OSCCONbits.LTS                  // bit 1
#define HTS                     OSCCONbits.HTS                  // bit 2
#define OSTS                    OSCCONbits.OSTS                 // bit 3
#define IRCF0                   OSCCONbits.IRCF0                // bit 4
#define IRCF1                   OSCCONbits.IRCF1                // bit 5
#define IRCF2                   OSCCONbits.IRCF2                // bit 6

#define TUN0                    OSCTUNEbits.TUN0                // bit 0
#define TUN1                    OSCTUNEbits.TUN1                // bit 1
#define TUN2                    OSCTUNEbits.TUN2                // bit 2
#define TUN3                    OSCTUNEbits.TUN3                // bit 3
#define TUN4                    OSCTUNEbits.TUN4                // bit 4

#define NOT_BOR                 PCONbits.NOT_BOR                // bit 0, shadows bit in PCONbits
#define NOT_BOD                 PCONbits.NOT_BOD                // bit 0, shadows bit in PCONbits
#define NOT_POR                 PCONbits.NOT_POR                // bit 1
#define SBODEN                  PCONbits.SBODEN                 // bit 4
#define ULPWUE                  PCONbits.ULPWUE                 // bit 5

#define TMR1IE                  PIE1bits.TMR1IE                 // bit 0, shadows bit in PIE1bits
#define T1IE                    PIE1bits.T1IE                   // bit 0, shadows bit in PIE1bits
#define TXIE                    PIE1bits.TXIE                   // bit 1
#define OSFIE                   PIE1bits.OSFIE                  // bit 2
#define C1IE                    PIE1bits.C1IE                   // bit 3
#define C2IE                    PIE1bits.C2IE                   // bit 4
#define RCIE                    PIE1bits.RCIE                   // bit 5
#define ADIE                    PIE1bits.ADIE                   // bit 6
#define EEIE                    PIE1bits.EEIE                   // bit 7

#define TMR1IF                  PIR1bits.TMR1IF                 // bit 0, shadows bit in PIR1bits
#define T1IF                    PIR1bits.T1IF                   // bit 0, shadows bit in PIR1bits
#define TXIF                    PIR1bits.TXIF                   // bit 1
#define OSFIF                   PIR1bits.OSFIF                  // bit 2
#define C1IF                    PIR1bits.C1IF                   // bit 3
#define C2IF                    PIR1bits.C2IF                   // bit 4
#define RCIF                    PIR1bits.RCIF                   // bit 5
#define ADIF                    PIR1bits.ADIF                   // bit 6
#define EEIF                    PIR1bits.EEIF                   // bit 7

#define RA0                     PORTAbits.RA0                   // bit 0
#define RA1                     PORTAbits.RA1                   // bit 1
#define RA2                     PORTAbits.RA2                   // bit 2
#define RA3                     PORTAbits.RA3                   // bit 3
#define RA4                     PORTAbits.RA4                   // bit 4
#define RA5                     PORTAbits.RA5                   // bit 5

#define RC0                     PORTCbits.RC0                   // bit 0
#define RC1                     PORTCbits.RC1                   // bit 1
#define RC2                     PORTCbits.RC2                   // bit 2
#define RC3                     PORTCbits.RC3                   // bit 3
#define RC4                     PORTCbits.RC4                   // bit 4
#define RC5                     PORTCbits.RC5                   // bit 5

#define RX9D                    RCSTAbits.RX9D                  // bit 0
#define OERR                    RCSTAbits.OERR                  // bit 1
#define FERR                    RCSTAbits.FERR                  // bit 2
#define ADDEN                   RCSTAbits.ADDEN                 // bit 3
#define CREN                    RCSTAbits.CREN                  // bit 4
#define SREN                    RCSTAbits.SREN                  // bit 5
#define RX9                     RCSTAbits.RX9                   // bit 6
#define SPEN                    RCSTAbits.SPEN                  // bit 7

#define C                       STATUSbits.C                    // bit 0
#define DC                      STATUSbits.DC                   // bit 1
#define Z                       STATUSbits.Z                    // bit 2
#define NOT_PD                  STATUSbits.NOT_PD               // bit 3
#define NOT_TO                  STATUSbits.NOT_TO               // bit 4
#define RP0                     STATUSbits.RP0                  // bit 5
#define RP1                     STATUSbits.RP1                  // bit 6
#define IRP                     STATUSbits.IRP                  // bit 7

#define TMR1ON                  T1CONbits.TMR1ON                // bit 0
#define TMR1CS                  T1CONbits.TMR1CS                // bit 1
#define NOT_T1SYNC              T1CONbits.NOT_T1SYNC            // bit 2
#define T1OSCEN                 T1CONbits.T1OSCEN               // bit 3
#define T1CKPS0                 T1CONbits.T1CKPS0               // bit 4
#define T1CKPS1                 T1CONbits.T1CKPS1               // bit 5
#define TMR1GE                  T1CONbits.TMR1GE                // bit 6
#define T1GINV                  T1CONbits.T1GINV                // bit 7

#define TRISA0                  TRISAbits.TRISA0                // bit 0
#define TRISA1                  TRISAbits.TRISA1                // bit 1
#define TRISA2                  TRISAbits.TRISA2                // bit 2
#define TRISA3                  TRISAbits.TRISA3                // bit 3
#define TRISA4                  TRISAbits.TRISA4                // bit 4
#define TRISA5                  TRISAbits.TRISA5                // bit 5

#define TRISC0                  TRISCbits.TRISC0                // bit 0
#define TRISC1                  TRISCbits.TRISC1                // bit 1
#define TRISC2                  TRISCbits.TRISC2                // bit 2
#define TRISC3                  TRISCbits.TRISC3                // bit 3
#define TRISC4                  TRISCbits.TRISC4                // bit 4
#define TRISC5                  TRISCbits.TRISC5                // bit 5

#define TX9D                    TXSTAbits.TX9D                  // bit 0
#define TRMT                    TXSTAbits.TRMT                  // bit 1
#define BRGH                    TXSTAbits.BRGH                  // bit 2
#define SENDB                   TXSTAbits.SENDB                 // bit 3
#define SYNC                    TXSTAbits.SYNC                  // bit 4
#define TXEN                    TXSTAbits.TXEN                  // bit 5
#define TX9                     TXSTAbits.TX9                   // bit 6
#define CSRC                    TXSTAbits.CSRC                  // bit 7

#define VR0                     VRCONbits.VR0                   // bit 0
#define VR1                     VRCONbits.VR1                   // bit 1
#define VR2                     VRCONbits.VR2                   // bit 2
#define VR3                     VRCONbits.VR3                   // bit 3
#define VRR                     VRCONbits.VRR                   // bit 5
#define VREN                    VRCONbits.VREN                  // bit 7

#define SWDTEN                  WDTCONbits.SWDTEN               // bit 0
#define WDTPS0                  WDTCONbits.WDTPS0               // bit 1
#define WDTPS1                  WDTCONbits.WDTPS1               // bit 2
#define WDTPS2                  WDTCONbits.WDTPS2               // bit 3
#define WDTPS3                  WDTCONbits.WDTPS3               // bit 4

#define WPUA0                   WPUbits.WPUA0                   // bit 0, shadows bit in WPUbits
#define WPU0                    WPUbits.WPU0                    // bit 0, shadows bit in WPUbits
#define WPUA1                   WPUbits.WPUA1                   // bit 1, shadows bit in WPUbits
#define WPU1                    WPUbits.WPU1                    // bit 1, shadows bit in WPUbits
#define WPUA2                   WPUbits.WPUA2                   // bit 2, shadows bit in WPUbits
#define WPU2                    WPUbits.WPU2                    // bit 2, shadows bit in WPUbits
#define WPUA4                   WPUbits.WPUA4                   // bit 4, shadows bit in WPUbits
#define WPU4                    WPUbits.WPU4                    // bit 4, shadows bit in WPUbits
#define WPUA5                   WPUbits.WPUA5                   // bit 5, shadows bit in WPUbits
#define WPU5                    WPUbits.WPU5                    // bit 5, shadows bit in WPUbits

#endif // #ifndef NO_BIT_DEFINES

#endif // #ifndef __PIC16F688_H__
